ShonP40/Car-Assistant/PCB/Photos/Enclosure/01 - Main.jpeg

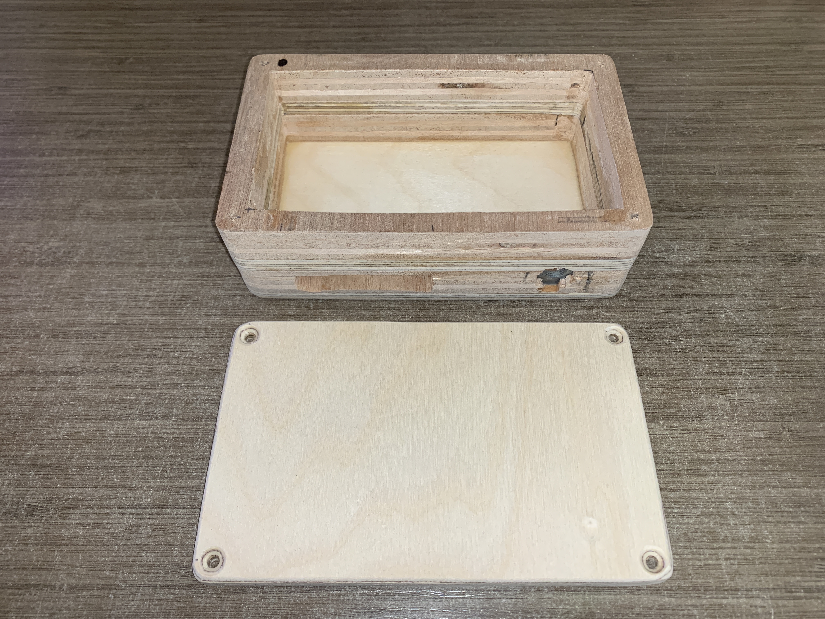
PCB/Photos/Enclosure/01 - Main.jpeg
