ShonP40/Car-Assistant/PCB/Photos/Enclosure/02 - Main (Lid).jpeg

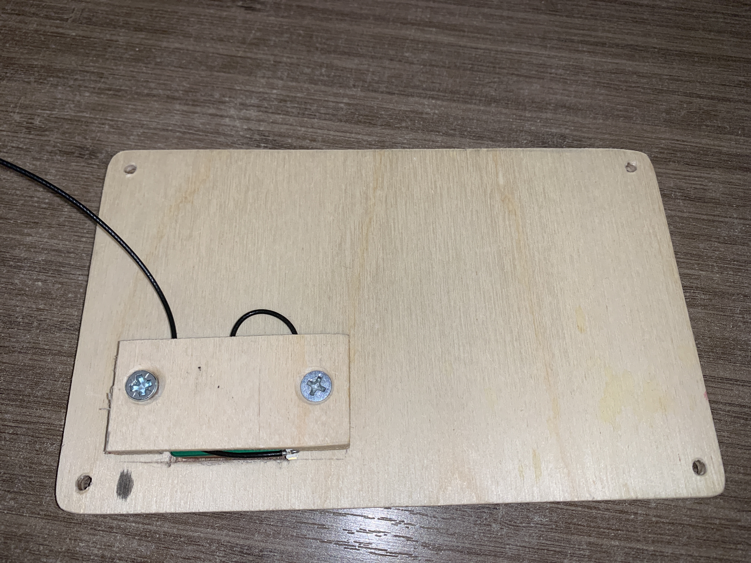
PCB/Photos/Enclosure/02 - Main (Lid).jpeg
