ShonP40/Car-Assistant/PCB/Photos/Enclosure/04 - Sensors.jpeg

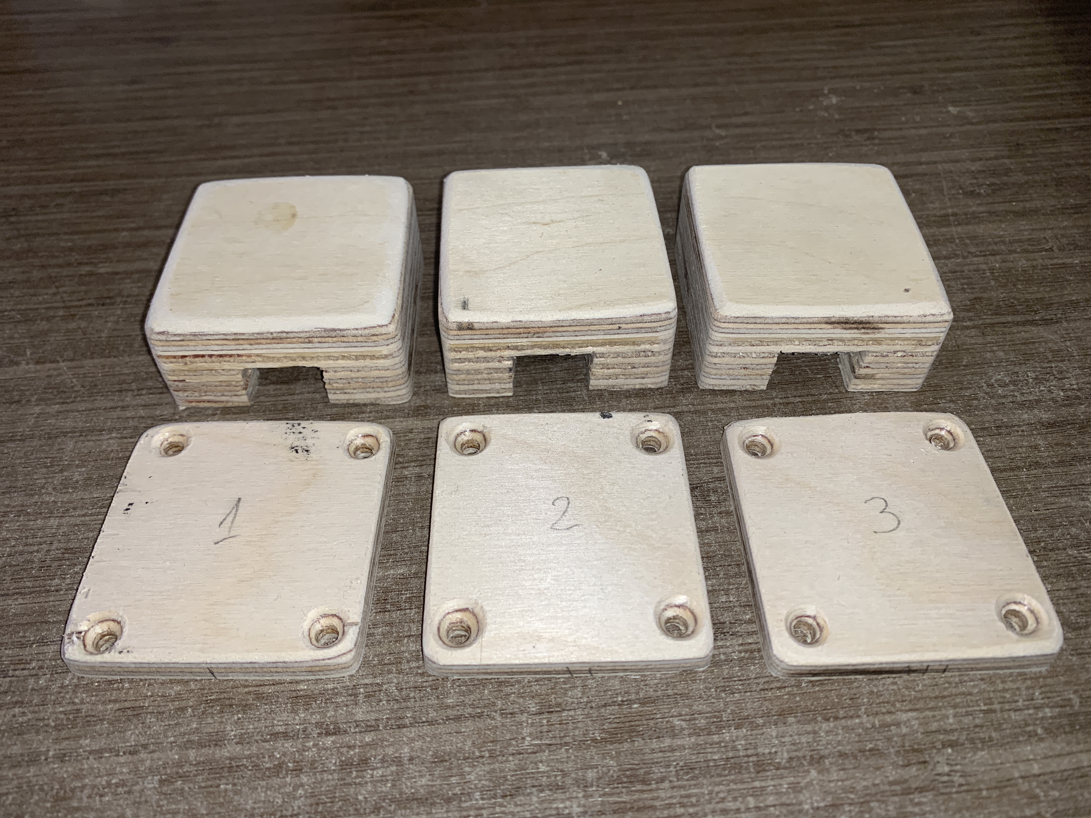
PCB/Photos/Enclosure/04 - Sensors.jpeg
