ShonP40/Car-Assistant/PCB/Photos/Enclosure/06 - Sensors (TSL2561).jpeg

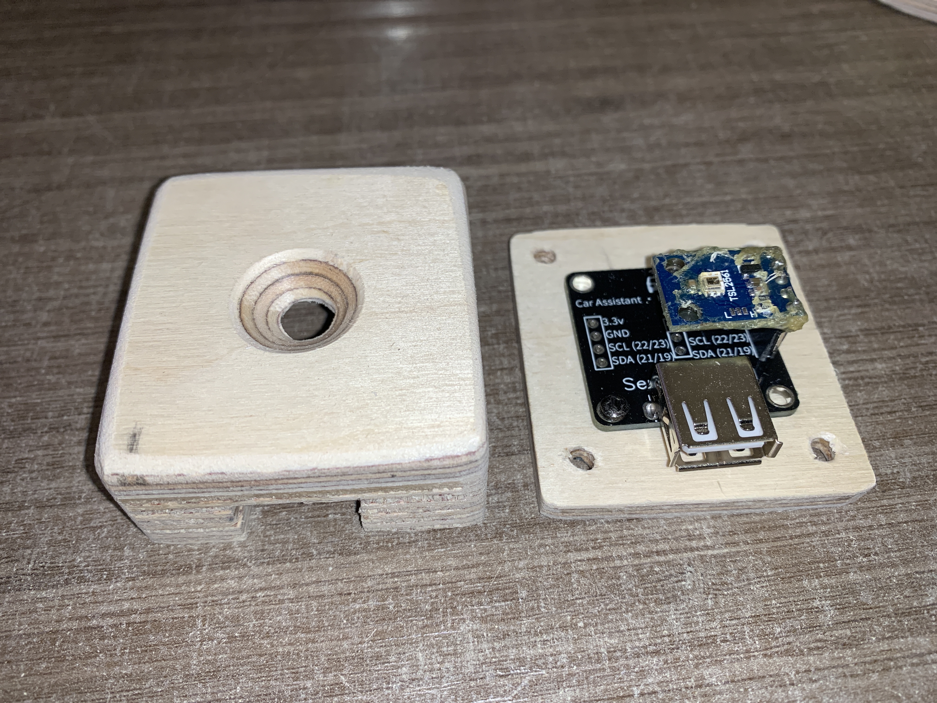
PCB/Photos/Enclosure/06 - Sensors (TSL2561).jpeg
