ShonP40/Car-Assistant/PCB/Photos/Enclosure/03 - Main (Assembled).jpeg

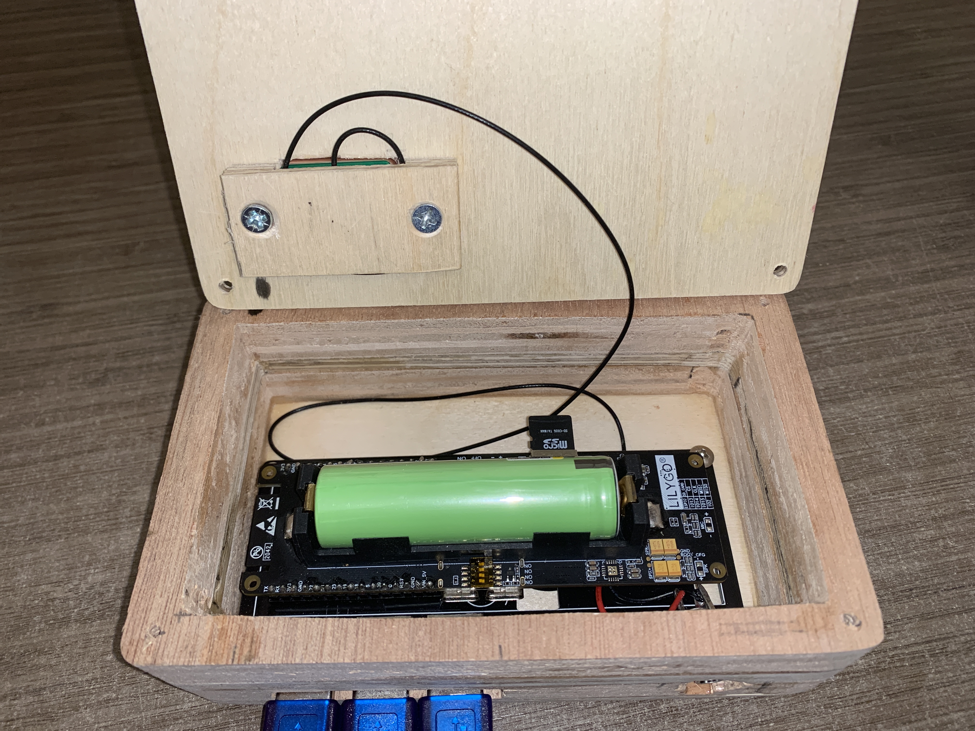
PCB/Photos/Enclosure/03 - Main (Assembled).jpeg
