ShonP40/Car-Assistant/PCB/Photos/Enclosure/08 - Sensors (BME280 - Assembled).jpeg

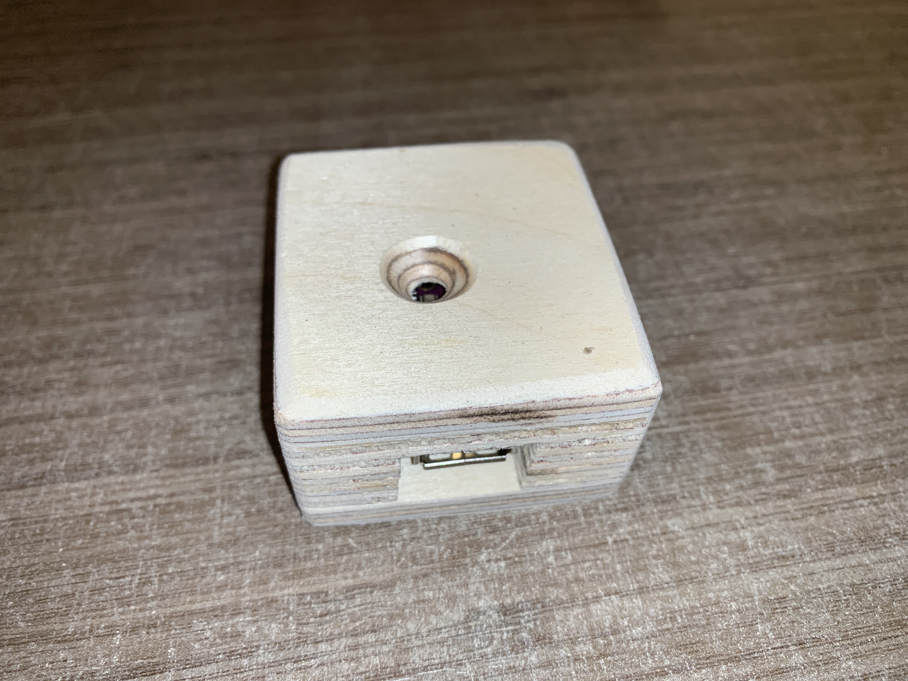
PCB/Photos/Enclosure/08 - Sensors (BME280 - Assembled).jpeg
