ShonP40/Car-Assistant/PCB/Photos/PCB/04 - Bottom Layer Soldered (Main).jpeg

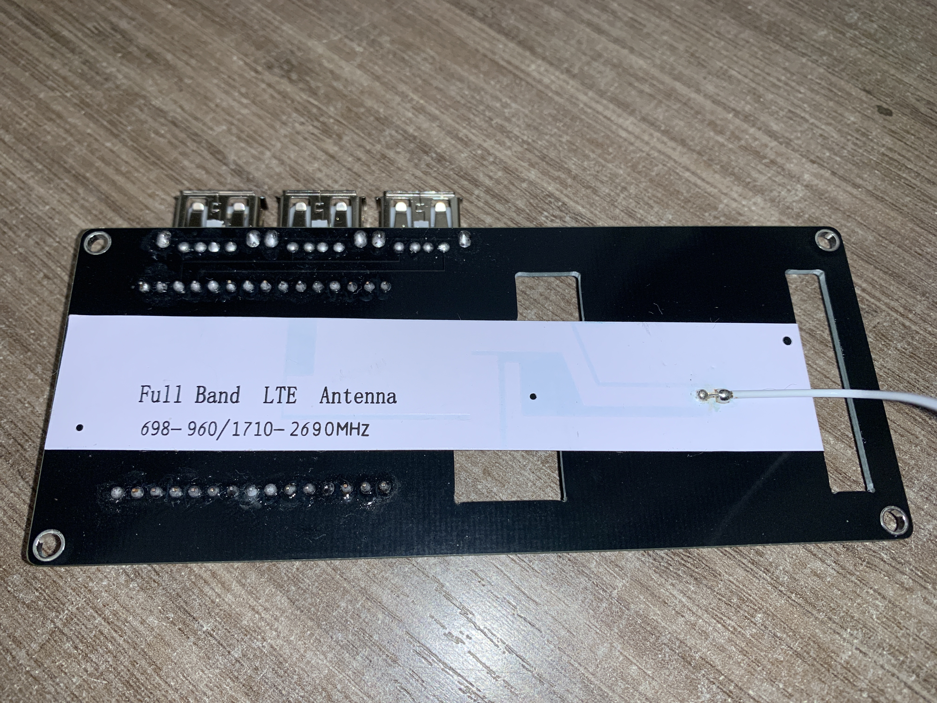
PCB/Photos/PCB/04 - Bottom Layer Soldered (Main).jpeg
