ShonP40/Car-Assistant/PCB/Photos/PCB/05 - Assembled (Main).jpeg

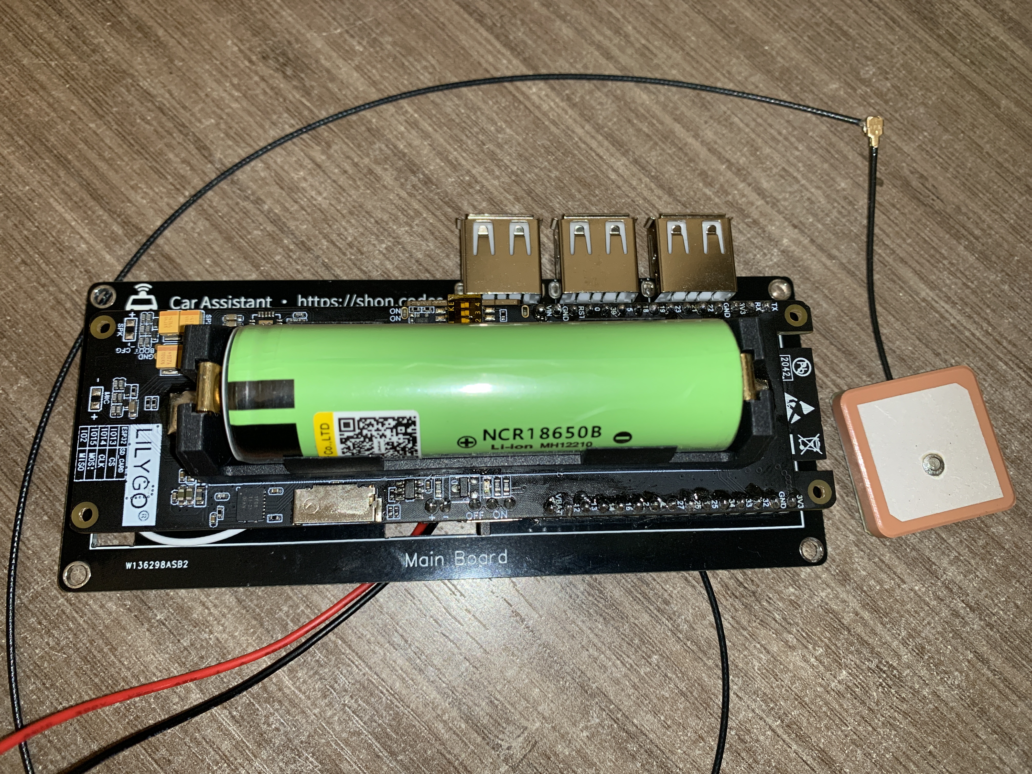
PCB/Photos/PCB/05 - Assembled (Main).jpeg
